theelims/SmartAssPlug/docs/img/PolishWire.jpg

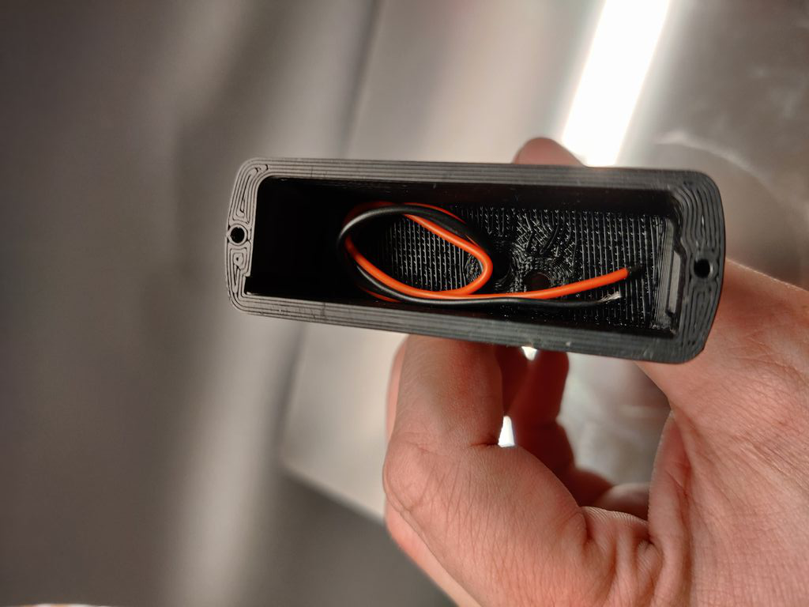
docs/img/PolishWire.jpg
